Yarnemeuris/RC-Transmitter/Firmware/bitmaps.ino

const byte PROGMEM BATTERY_IOCN[5] = { 0b01111111, 0b11000001, 0b11000001, 0b11000001, 0b01111111 };

const byte PROGMEM DIGITS[10][5] = { { 0b11100000, 0b10100000, 0b10100000, 0b10100000, 0b11100000 }, { 0b00100000, 0b00100000, 0b00100000, 0b00100000, 0b00100000 }, { 0b11100000, 0b00100000, 0b11100000, 0b10000000, 0b11100000 }, { 0b11100000, 0b00100000, 0b11100000, 0b00100000, 0b11100000 }, { 0b10100000, 0b10100000, 0b11100000, 0b00100000, 0b00100000 }, { 0b11100000, 0b10000000, 0b11100000, 0b00100000, 0b11100000 }, { 0b11100000, 0b10000000, 0b11100000, 0b10100000, 0b11100000 }, { 0b11100000, 0b00100000, 0b00100000, 0b00100000, 0b00100000 }, { 0b11100000, 0b10100000, 0b11100000, 0b10100000, 0b11100000 }, { 0b11100000, 0b10100000, 0b11100000, 0b00100000, 0b00100000 } };
const byte PROGMEM PERCENT[5] = { 0b10000000, 0b00100000, 0b01000000, 0b10000000, 0b00100000 };
